elpayocabra/dioptra-digital/photo_2025-09-05_14-11-01.jpg

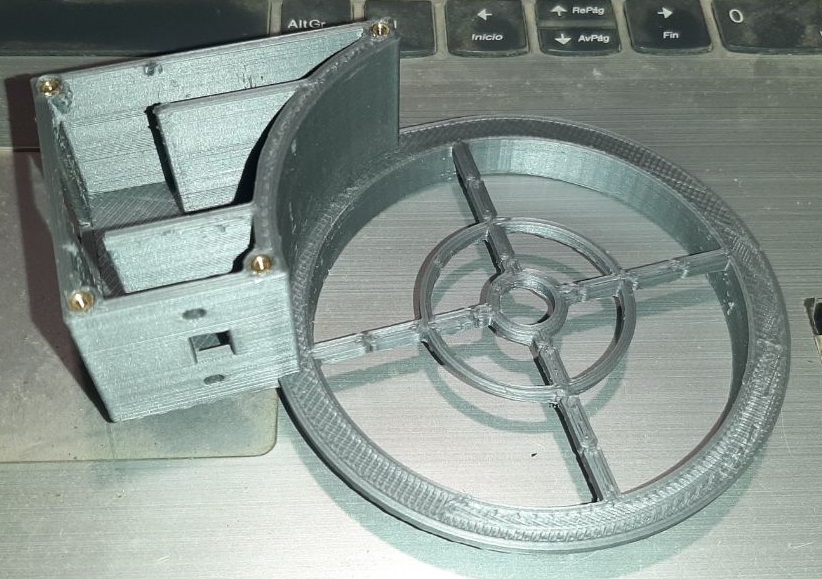
photo_2025-09-05_14-11-01.jpg
