elpayocabra/dioptra-digital/photo_2025-09-05_14-11-04 (2).jpg

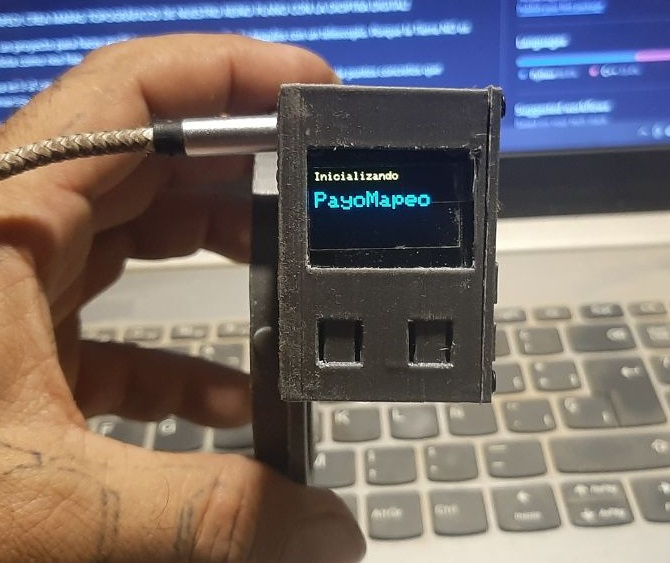
photo_2025-09-05_14-11-04 (2).jpg
