elpayocabra/dioptra-digital/photo_2025-09-05_14-12-50.jpg

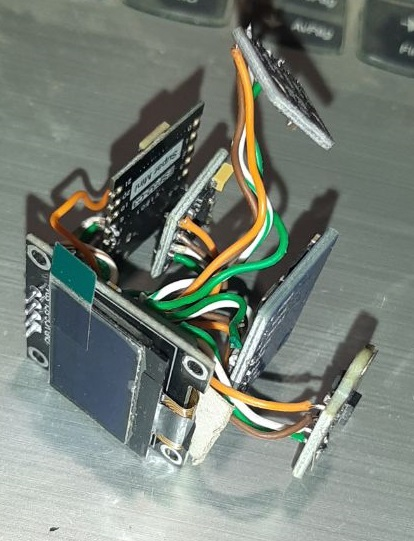
photo_2025-09-05_14-12-50.jpg
