elpayocabra/dioptra-digital/photo_2025-09-05_14-58-33.jpg

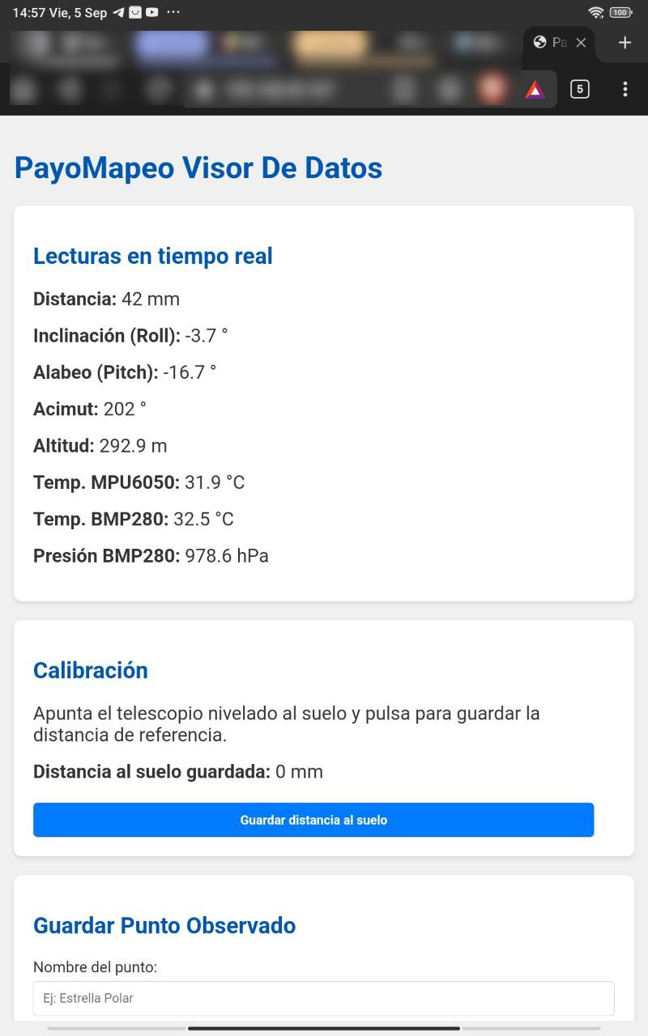
photo_2025-09-05_14-58-33.jpg
