elpayocabra/dioptra-digital/photo_2025-09-05_15-30-03.jpg

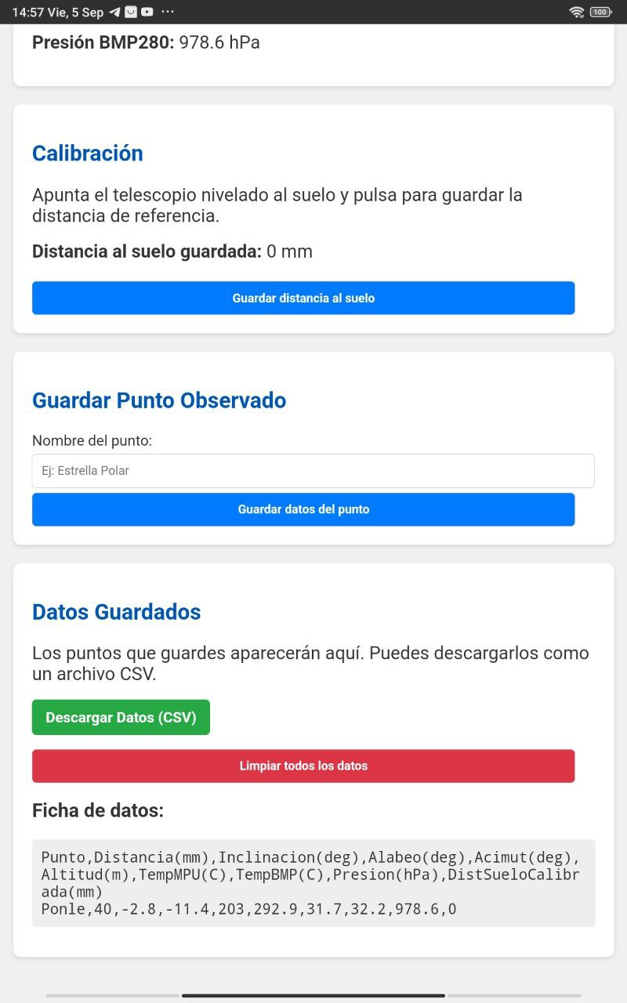
photo_2025-09-05_15-30-03.jpg
